sevikkk/valurap/zcad/examples/vitamins.png

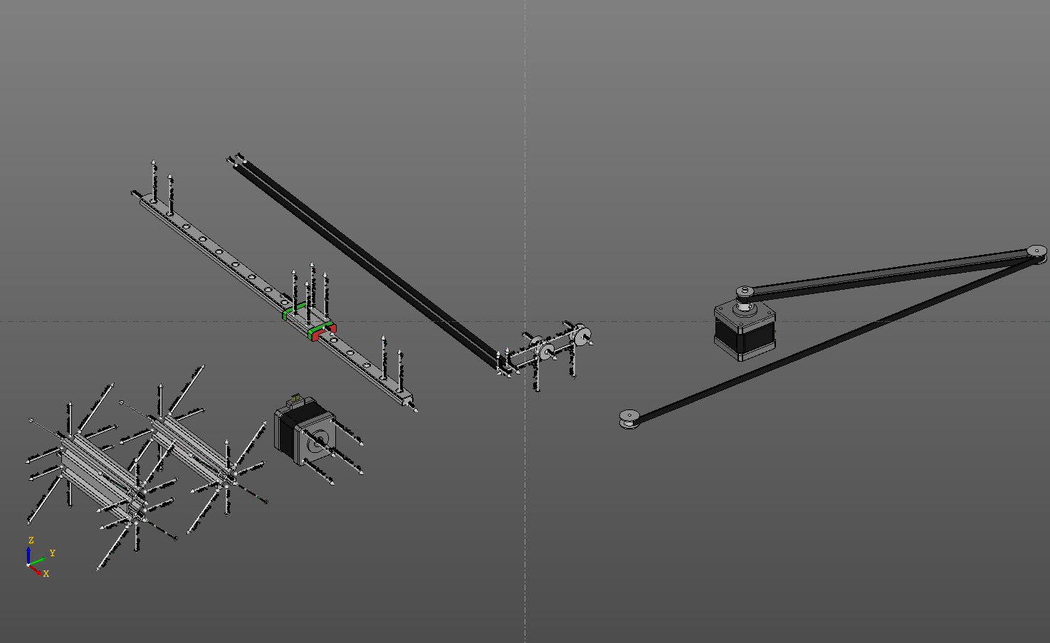
zcad/examples/vitamins.png
