sevikkk/valurap/freecad/vitamins/tcst2103.FCStd

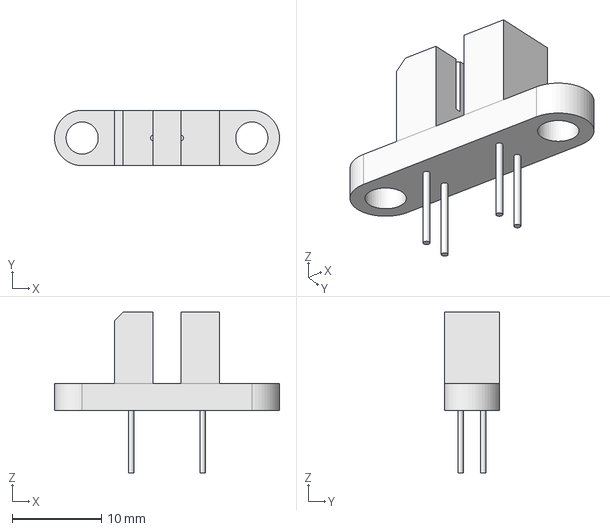
[picture p22: CAD file, 2019-09-13]
freecad/vitamins/tcst2103.FCStd
25.2 x 6.20 x 18.0 mm
