sevikkk/valurap/freecad/steppers_board_mount.FCStd

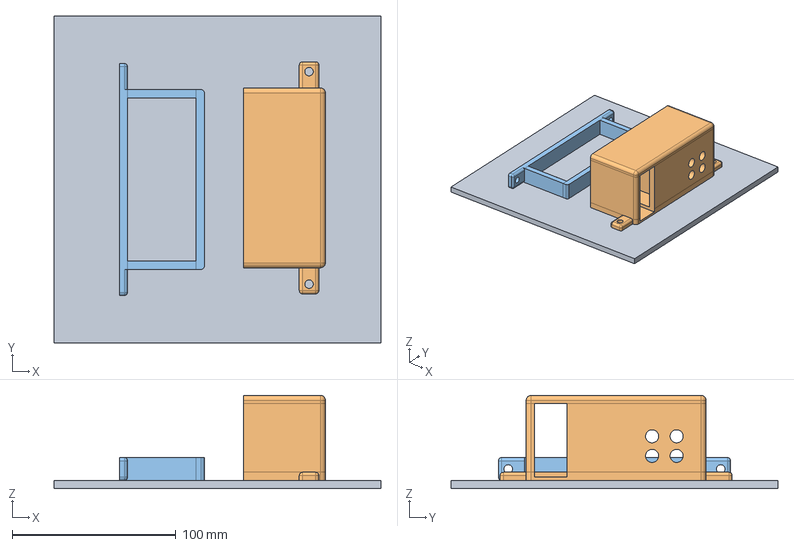
[picture p23: CAD file, 2019-10-19]
freecad/steppers_board_mount.FCStd
200.0 x 200.0 x 57.0 mm
print_plate
psu_front_mount_print
psu_back_mount_print
