sevikkk/valurap/freecad/vitamins/gp1s51.FCStd

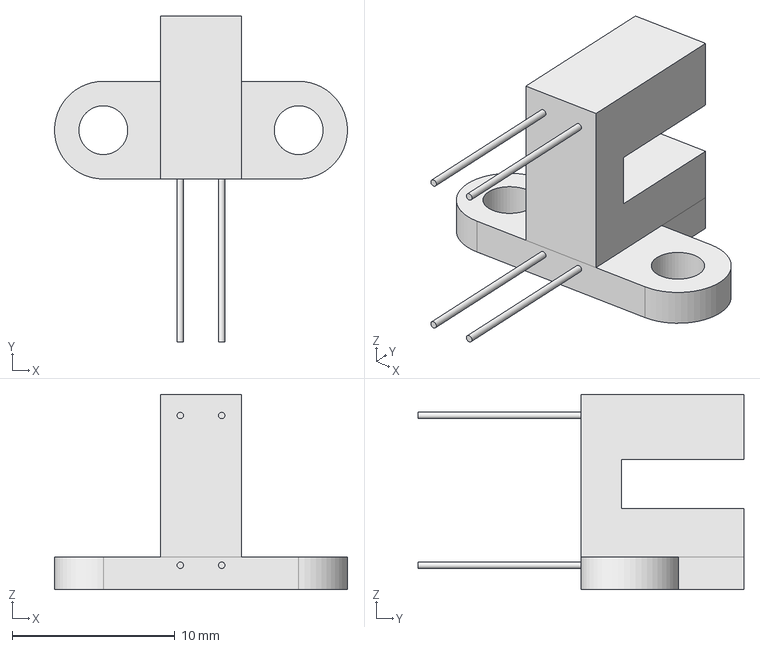
[picture p24: CAD file, 2019-09-01]
freecad/vitamins/gp1s51.FCStd
18.0 x 20.0 x 12.0 mm
