sevikkk/valurap/freecad/titan_mount_plate.FCStd

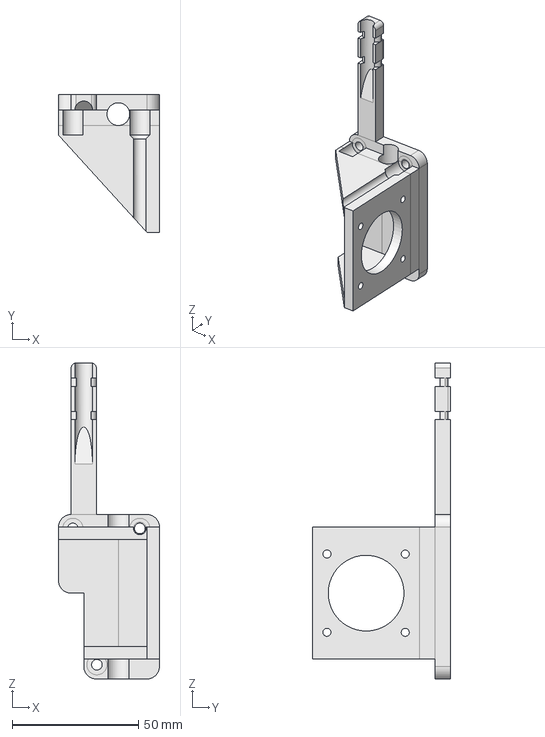
[picture p25: CAD file, 2019-10-13]
freecad/titan_mount_plate.FCStd
40.0 x 54.5 x 125.2 mm
