sevikkk/valurap/freecad/vitamins/coupler.FCStd

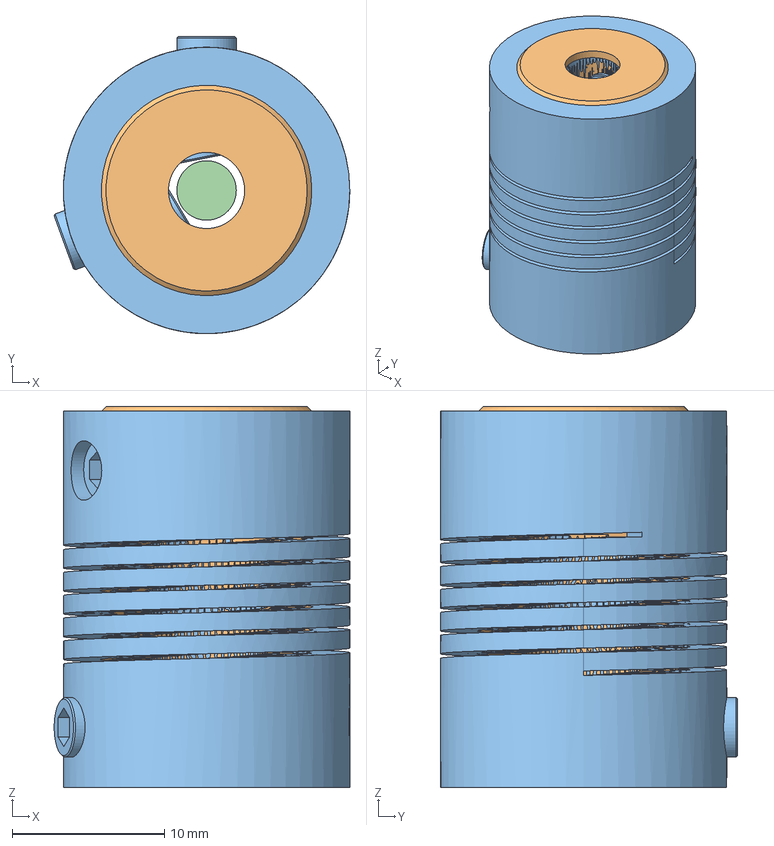
[picture p26: CAD file, 2019-09-01]
freecad/vitamins/coupler.FCStd
19.4 x 19.5 x 25.0 mm
coupling-compound
setscrew-body
