sevikkk/valurap/freecad/left_y_idler_plate.FCStd

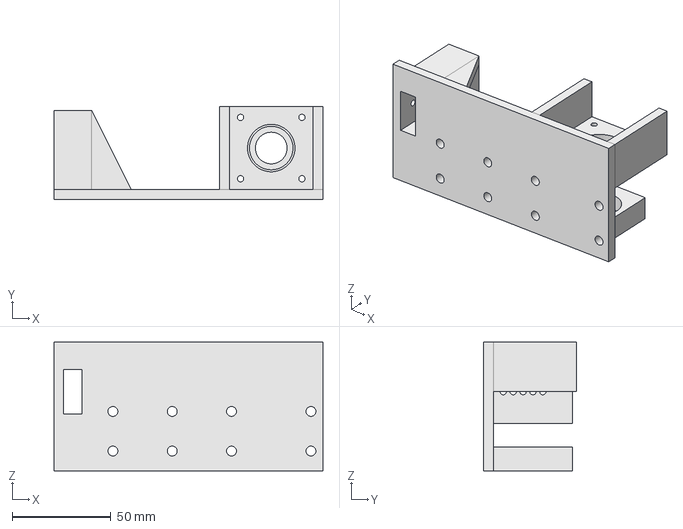
[picture p27: CAD file, 2019-10-13]
freecad/left_y_idler_plate.FCStd
135.9 x 47.0 x 65.0 mm
