sevikkk/valurap/freecad/x_carriage_plate.FCStd

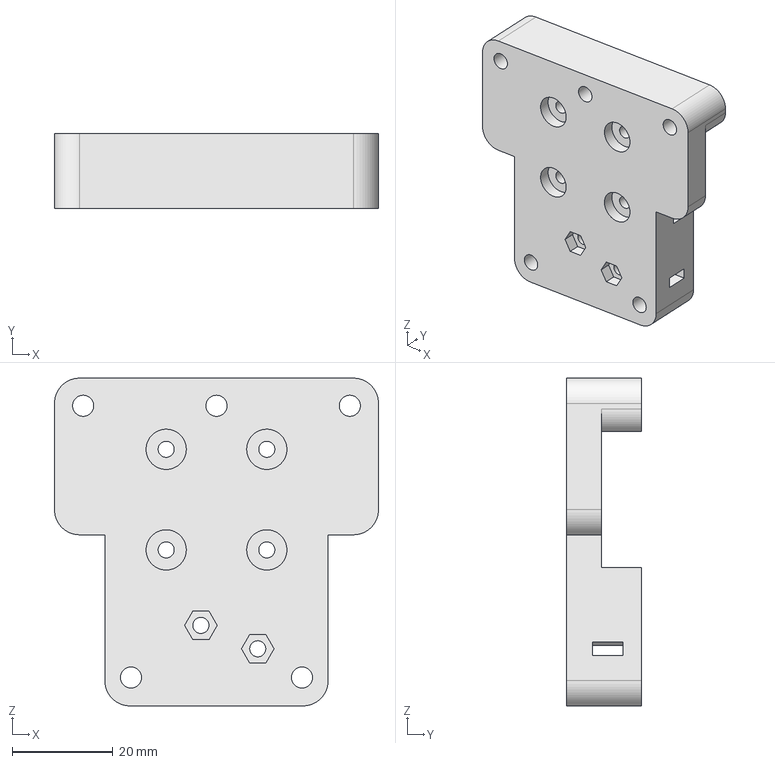
[picture p28: CAD file, 2019-10-13]
freecad/x_carriage_plate.FCStd
64.4 x 15.0 x 65.2 mm
