sevikkk/valurap/scad/prints-x-end.scad

include <x-end-plate.scad>

translate([0,0,-12.5]) rotate([0,0,0]) x_end_plate(25, 14, 25, 3);
translate([90,0,-35]) rotate([0,0,0]) x_end_top(25, 14, 25, 3);
