sevikkk/valurap/stm_soft/stm_thermo/code/task_thermo.c

//
// Created by Vsevolod Lobko on 02.11.2019.
//

#include <stdio.h>
#include <math.h>

int __errno;

#include "main.h"
#include "cmsis_os.h"
#include "cmdline.h"
#include "hardware.h"

volatile int32_t pid_targets[3] = {0, 0, 0};
volatile double pid_integrals[3];
volatile int32_t pid_k_i[3] = {400, 400, 400};
volatile int32_t pid_k_p[3] = {20000, 20000, 20000};

volatile int32_t k_type_temp = 0;
volatile int32_t adc_reads[5];
volatile int32_t ext_values[3];
volatile int32_t fan_values[3];
volatile int32_t adc_temps[3];
volatile int32_t heatbed_value = 0;

int32_t ech_ids[3] = {
    TIM_CHANNEL_1,
    TIM_CHANNEL_2,
    TIM_CHANNEL_3,
};

int32_t fch_ids[3] = {
    TIM_CHANNEL_3,
    TIM_CHANNEL_2,
    TIM_CHANNEL_1,
};

void set_fan_value(int32_t ch, int32_t val);

void StartThermoRead(void const* argument) {
    uint8_t in_buffer[2];
    uint8_t out_buffer[2];
    uint32_t adc_vals[5];
    uint32_t channels[5] = {ADC_CHANNEL_0, ADC_CHANNEL_4, ADC_CHANNEL_5,
                            ADC_CHANNEL_TEMPSENSOR, ADC_CHANNEL_VREFINT};
    ADC_ChannelConfTypeDef sConfig = {0};
    int i, j;

    TickType_t last_wake;

#define PID_CYCLE 400
#define PID_ADC_SUPERSAMPLE 250

    last_wake = xTaskGetTickCount() + 33;

    for (;;) {
        HAL_GPIO_WritePin(SPI1_NSS_GPIO_Port, SPI1_NSS_Pin, GPIO_PIN_RESET);
        HAL_SPI_TransmitReceive(&hspi1, out_buffer, in_buffer, 2, 1000);
        HAL_GPIO_WritePin(SPI1_NSS_GPIO_Port, SPI1_NSS_Pin, GPIO_PIN_SET);
        k_type_temp = (((uint32_t)in_buffer[0] << 8u) | (uint32_t)in_buffer[1]);

        for (i = 0; i < 5; i++) adc_vals[i] = 0;

        for (j = 0; j < PID_ADC_SUPERSAMPLE; j++)
            for (i = 0; i < 5; i++) {
                sConfig.Channel = channels[i];
                sConfig.Rank = ADC_REGULAR_RANK_1;
                sConfig.SamplingTime = ADC_SAMPLETIME_41CYCLES_5;
                HAL_ADC_ConfigChannel(&hadc1, &sConfig);
                HAL_ADC_Start(&hadc1);
                if (HAL_ADC_PollForConversion(&hadc1, 1000000) == HAL_OK) {
                    adc_vals[i] += HAL_ADC_GetValue(&hadc1);
                } else {
                    adc_vals[i] += 9999;
                }
                HAL_ADC_Stop(&hadc1);
            }

        for (i = 0; i < 5; i++) {
            adc_reads[i] = adc_vals[i] / PID_ADC_SUPERSAMPLE;
        }

        for (i = 0; i < 3; i++) {
            double adc = (double) adc_vals[i] / (double)PID_ADC_SUPERSAMPLE;
            // ext1: 10211.569233868902 4.081041224040854 -292.90712330869326 -2194.2350864642244

            double temp = (10157.98 + 4.051241 * adc - 290.5820 * sqrt(adc) - adc * adc/2209.283)/32.0;
            adc_temps[i] = (long)temp;

            double pid_error = (double)pid_targets[i] - temp;
            int control_value = 0;

            if (pid_error > 20) {
                control_value = 1000;
                pid_integrals[i] = 2500;
            } else if (pid_error < -20) {
                control_value = 0;
                pid_integrals[i] = 0;
            } else {
                double new_pid_integral = pid_integrals[i];

                new_pid_integral += pid_error;

                if (new_pid_integral > 5000.0) new_pid_integral = 5000.0;
                if (new_pid_integral < -5000.0) new_pid_integral = -5000.0;

                pid_integrals[i] = new_pid_integral;
                control_value = (long)(new_pid_integral * pid_k_i[i] + pid_error * pid_k_p[i]) / 1000;
            }
            if (control_value > 970) control_value = 1000;
            if (control_value < 10) control_value = 0;

            if (i < 2)
                __HAL_TIM_SET_COMPARE(&htim3, ech_ids[i], control_value);
            else
                heatbed_value = control_value;
        }

        for (i = 0; i < 3; i++) {
            ext_values[i] = __HAL_TIM_GET_COMPARE(&htim3, ech_ids[i]);
            fan_values[i] = __HAL_TIM_GET_COMPARE(&htim1, fch_ids[i]);
        }
        vTaskDelayUntil(&last_wake, PID_CYCLE);
    }
}

void StartHeatBedPWM(void const* argument) {
    TickType_t last_wake;
    int32_t current_cycle = 0;
#define HEATBED_CYCLE 5000

    last_wake = xTaskGetTickCount() + 33;

    for (;;) {
        current_cycle = heatbed_value * HEATBED_CYCLE / 1000;
        if (current_cycle >= HEATBED_CYCLE - 10) {
            HAL_GPIO_WritePin(GPIOC, GPIO_PIN_14, GPIO_PIN_SET);
            vTaskDelayUntil(&last_wake, HEATBED_CYCLE);
        } else if (current_cycle > 10) {
            HAL_GPIO_WritePin(GPIOC, GPIO_PIN_14, GPIO_PIN_SET);
            vTaskDelayUntil(&last_wake, current_cycle);
            HAL_GPIO_WritePin(GPIOC, GPIO_PIN_14, GPIO_PIN_RESET);
            vTaskDelayUntil(&last_wake, HEATBED_CYCLE - current_cycle);
        } else {
            HAL_GPIO_WritePin(GPIOC, GPIO_PIN_14, GPIO_PIN_RESET);
            vTaskDelayUntil(&last_wake, HEATBED_CYCLE);
        };
    }
}

void sepFunction(void) {
    int32_t psc;
    psc = cmdlineGetArgInt(1);
    __HAL_TIM_SET_PRESCALER(&htim3, psc);
}

void sfpFunction(void) {
    int32_t psc;
    psc = cmdlineGetArgInt(1);
    __HAL_TIM_SET_PRESCALER(&htim1, psc);
}

void sevFunction(void) {
    int32_t ch;
    int32_t val;

    ch = cmdlineGetArgInt(1);
    val = cmdlineGetArgInt(2);
    if (ch > 0 && ch <= 3) __HAL_TIM_SET_COMPARE(&htim3, ech_ids[ch - 1], val);
}

void sfvFunction(void) {
    int32_t ch;
    int32_t val;

    ch = cmdlineGetArgInt(1);
    val = cmdlineGetArgInt(2);
    if (ch > 0 && ch <= 3) set_fan_value(ch, val);
}

void set_fan_value(int32_t ch, int32_t val) { __HAL_TIM_SET_COMPARE(&htim1, fch_ids[ch - 1], val); }

void sptFunction(void) {
    int32_t ch;
    int32_t val;

    ch = cmdlineGetArgInt(1);
    val = cmdlineGetArgInt(2);
    if (ch > 0 && ch <= 3) {
        pid_targets[ch - 1] = val;
        pid_integrals[ch - 1] = 0;
    }
}

void sppFunction(void) {
    int32_t ch;
    int32_t val_p;
    int32_t val_i;

    ch = cmdlineGetArgInt(1);
    val_p = cmdlineGetArgInt(2);
    val_i = cmdlineGetArgInt(3);
    if (ch > 0 && ch <= 3) {
        pid_k_p[ch - 1] = val_p;
        pid_k_i[ch - 1] = val_i;
        pid_integrals[ch - 1] = 0;
    }
}

void shpidFunction(void) {
    int32_t ch;

    ch = cmdlineGetArgInt(1);
    if (ch <= 0 || ch > 3) return;

    printf("pid_k_p: %ld\n", pid_k_p[ch - 1]);
    printf("pid_k_i: %ld\n", pid_k_i[ch - 1]);
    printf("integral: %ld\n", (long)pid_integrals[ch - 1]);
    fflush(0);
}
