sevikkk/valurap/fpga/src/s3g_executor.v

module s3g_executor(
    input clk,
    input rst,

    // s3g_rx interface
    input rx_packet_done,
    input rx_packet_error,
    input rx_buffer_valid,

    input [7:0] rx_payload_len,
    input [7:0] rx_buf0,
    input [7:0] rx_buf1,
    input [7:0] rx_buf2,
    input [7:0] rx_buf3,
    input [7:0] rx_buf4,
    input [7:0] rx_buf5,
    input [7:0] rx_buf6,
    input [7:0] rx_buf7,
    input [7:0] rx_buf8,
    input [7:0] rx_buf9,
    input [7:0] rx_buf10,
    input [7:0] rx_buf11,
    input [7:0] rx_buf12,
    input [7:0] rx_buf13,
    input [7:0] rx_buf14,
    input [7:0] rx_buf15,

    output reg [7:0] next_rx_buffer_addr,
    input [7:0] rx_buffer_data,

    // s3g_tx interface
    input tx_busy,
    output reg tx_packet_wr,

    output reg [7:0] tx_payload_len,
    output reg [7:0] tx_buf0,
    output reg [7:0] tx_buf1,
    output reg [7:0] tx_buf2,
    output reg [7:0] tx_buf3,
    output reg [7:0] tx_buf4,
    output reg [7:0] tx_buf5,
    output reg [7:0] tx_buf6,
    output reg [7:0] tx_buf7,
    output reg [7:0] tx_buf8,
    output reg [7:0] tx_buf9,
    output reg [7:0] tx_buf10,
    output reg [7:0] tx_buf11,
    output reg [7:0] tx_buf12,
    output reg [7:0] tx_buf13,
    output reg [7:0] tx_buf14,
    output reg [7:0] tx_buf15,

    // output_registers
    output reg [31:0] out_reg0,
    output reg [31:0] out_reg1,
    output reg [31:0] out_reg2,
    output reg [31:0] out_reg3,
    output reg [31:0] out_reg4,
    output reg [31:0] out_reg5,
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
    input int21,
    input int22,
    input int23,
    input int24,
    input int25,
    input int26,
    input int27,
    input int28,
    input int29,
    input int30,
    input int31,

    output reg [39:0] ext_fifo_data,
    output reg ext_fifo_wr,
    input [31:0] ext_fifo_free_space,

    input [5:0] ext_out_reg_addr,
    input [31:0] ext_out_reg_data,
    input ext_out_reg_stb,
    output ext_out_reg_busy,
    input [31:0] ext_out_stbs,
    input [31:0] ext_clear_ints,
    output [31:0] ext_pending_ints
);

    parameter EXT_VER_1=8'h02;
    parameter EXT_VER_2=8'h00;
    parameter EXT_VER_3=8'h02;
    parameter EXT_VER_4=8'h00;
    parameter EXT_VER_5=8'hCE;
    parameter EXT_VER_6=8'h00;
    parameter EXT_VER_7=8'h00;
    parameter EXT_VER_8=8'h00;

    localparam
        CMD_NONE=0, CMD_OK=1, CMD_ERROR=2, CMD_UNKNOWN=3, CMD_READ_REG=4,
        CMD_VERSION=5, CMD_EXT_VERSION=6, CMD_WR_BUF_OK=8, CMD_WR_BUF_ERR=9;

    localparam
        S_INIT=0, S_DELAY=1, S_BUSY=2, S_READ=3, S_READ1=4,
        S_BUFFER0=5, S_BUFFER1=6, S_BUFFER2=7, S_BUFFER3=8,
        S_BUFFER4=9, S_BUFFER5=10, S_BUFFER6=11, S_BUFFER_WAIT=12;

    reg [3:0] state = S_INIT;
    reg [3:0] next_state;

    reg [3:0] tx_cmd;
    reg [3:0] next_tx_cmd;

    reg [5:0] int_out_reg_addr;
    reg [31:0] int_out_reg_data;
    reg int_out_reg_stb;

    wire [5:0] out_reg_addr;
    wire [31:0] out_reg_data;
    wire out_reg_stb;

    reg [31:0] next_out_stbs;

    reg [5:0] next_in_mux;
    reg [5:0] in_mux;
    reg [31:0] in_data;

    wire [31:0] ints_vector;
    reg [31:0] ints_pending;
    reg [31:0] ints_mask;
    reg [31:0] next_ints_mask;
    reg [31:0] ints_to_clear;

    reg [7:0] rx_buffer_addr;
    reg [39:0] next_ext_fifo_data;
    reg next_ext_fifo_wr;

    reg [7:0] word_cnt;
    reg [7:0] next_word_cnt;

    reg [15:0] saved_cmd_id;
    reg [15:0] next_saved_cmd_id;

    assign ints_vector = {
        int31, int30, int29, int28, int27, int26, int25, int24,
        int23, int22, int21, int20, int19, int18, int17, int16,
        int15, int14, int13, int12, int11, int10, int9, int8,
        int7, int6, int5, int4, int3, int2, int1, int0};

    always @(posedge clk)
        begin
            if (rst)
                ints_pending <= 0;
            else
                ints_pending <= (ints_pending & ~(ints_to_clear | ext_clear_ints)) | ints_vector;
        end

    assign ext_pending_ints = ints_pending;

    always @(posedge clk)
        begin
            if (rst)
                begin
                    out_stbs <= 0;
                    ints_mask <= 32'hFFFFFFFF;
                    in_mux <= 0;
                    rx_buffer_addr <= 0;
                    word_cnt <= 0;
                    ext_fifo_data <= 0;
                    ext_fifo_wr <= 0;
                    saved_cmd_id <= 16'hFFFF;
                    tx_cmd <= CMD_NONE;
                end
            else
                begin
                    out_stbs <= next_out_stbs | ext_out_stbs;
                    ints_mask <= next_ints_mask;
                    in_mux <= next_in_mux;
                    rx_buffer_addr <= next_rx_buffer_addr;
                    word_cnt <= next_word_cnt;
                    ext_fifo_data <= next_ext_fifo_data;
                    ext_fifo_wr <= next_ext_fifo_wr;
                    saved_cmd_id <= next_saved_cmd_id;
                    tx_cmd <= next_tx_cmd;
                end

            in_data <= 0;
            case (in_mux)
                0: in_data <= in_reg0;
                1: in_data <= in_reg1;
                2: in_data <= in_reg2;
                3: in_data <= in_reg3;
                4: in_data <= in_reg4;
                5: in_data <= in_reg5;
                6: in_data <= in_reg6;
                7: in_data <= in_reg7;
                8: in_data <= in_reg8;
                9: in_data <= in_reg9;
                10: in_data <= in_reg10;
                11: in_data <= in_reg11;
                12: in_data <= in_reg12;
                13: in_data <= in_reg13;
                14: in_data <= in_reg14;
                15: in_data <= in_reg15;
                16: in_data <= in_reg16;
                17: in_data <= in_reg17;
                18: in_data <= in_reg18;
                19: in_data <= in_reg19;
                20: in_data <= in_reg20;
                21: in_data <= in_reg21;
                22: in_data <= in_reg22;
                23: in_data <= in_reg23;
                24: in_data <= in_reg24;
                25: in_data <= in_reg25;
                26: in_data <= in_reg26;
                27: in_data <= in_reg27;
                28: in_data <= in_reg28;
                29: in_data <= in_reg29;
                30: in_data <= in_reg30;
                31: in_data <= in_reg31;
                32: in_data <= in_reg32;
                33: in_data <= in_reg33;
                34: in_data <= in_reg34;
                35: in_data <= in_reg35;
                36: in_data <= in_reg36;
                37: in_data <= in_reg37;
                38: in_data <= in_reg38;
                39: in_data <= in_reg39;
                40: in_data <= in_reg40;
                41: in_data <= in_reg41;
                42: in_data <= in_reg42;
                43: in_data <= in_reg43;
                44: in_data <= in_reg44;
                45: in_data <= in_reg45;
                46: in_data <= in_reg46;
                47: in_data <= in_reg47;
                48: in_data <= in_reg48;
                49: in_data <= in_reg49;
                50: in_data <= in_reg50;
                51: in_data <= in_reg51;
                52: in_data <= in_reg52;
                53: in_data <= in_reg53;
                54: in_data <= in_reg54;
                55: in_data <= in_reg55;
                56: in_data <= in_reg56;
                57: in_data <= in_reg57;
                58: in_data <= in_reg58;
                59: in_data <= in_reg59;
                60: in_data <= in_reg60;
                61: in_data <= in_reg61;
                62: in_data <= in_reg62;
                63: in_data <= in_reg63;
            endcase
        end

    always @(*)
        begin
            next_state <= state;
            next_tx_cmd <= CMD_NONE;
            next_in_mux <= in_mux;
            next_out_stbs <= 0;

            next_ints_mask <= ints_mask;

            int_out_reg_stb <= 0;
            int_out_reg_addr <= 0;
            int_out_reg_data <= 0;

            ints_to_clear <= 0;

            next_rx_buffer_addr <= rx_buffer_addr;
            next_word_cnt <= word_cnt;
            next_ext_fifo_data <= ext_fifo_data;
            next_ext_fifo_wr <= 0;

            next_saved_cmd_id <= saved_cmd_id;

            case (state)
                S_INIT:
                    begin
                        if (rx_packet_done)
                            begin
                                next_tx_cmd <= CMD_UNKNOWN;
                                next_state <= S_DELAY;
                                next_saved_cmd_id <= {rx_buf1, rx_buf0};
                                if (rx_payload_len == 0)
                                    begin
                                        next_tx_cmd <= CMD_OK;
                                    end
                                else
                                    case (rx_buf2)
                                        0:
                                            next_tx_cmd <= CMD_VERSION;
                                        27:
                                            next_tx_cmd <= CMD_EXT_VERSION;
                                        60: // WRITE_OUT_REG
                                            begin
                                                int_out_reg_stb <= 1;
                                                int_out_reg_addr <= rx_buf3;
                                                int_out_reg_data <= {rx_buf7, rx_buf6, rx_buf5, rx_buf4};
                                                next_tx_cmd <= CMD_OK;
                                            end
                                        61: // READ_IN_REG
                                            begin
                                                next_in_mux <= rx_buf3;
                                                next_state <= S_READ;
                                                next_tx_cmd <= CMD_NONE;
                                            end
                                        62: // OUT_STBS
                                            begin
                                                next_out_stbs <= {rx_buf6, rx_buf5, rx_buf4, rx_buf3};
                                                next_tx_cmd <= CMD_OK;
                                            end
                                        63: // CLEAR_INTS
                                            begin
                                                ints_to_clear <= {rx_buf6, rx_buf5, rx_buf4, rx_buf3};
                                                next_tx_cmd <= CMD_OK;
                                            end
                                        64: // MASK_INTS
                                            begin
                                                next_ints_mask <= {rx_buf6, rx_buf5, rx_buf4, rx_buf3};
                                                next_tx_cmd <= CMD_OK;
                                            end
                                        // 65: Not implemented
                                        66: // WRITE_FIFO
                                            begin
                                                next_rx_buffer_addr <= 4;
                                                next_word_cnt <= rx_buf3;
                                                if (rx_buf3 == 0)
                                                    begin
                                                        next_state <= S_DELAY;
                                                        next_tx_cmd <= CMD_WR_BUF_OK;
                                                    end
                                                else
                                                    begin
                                                        next_tx_cmd <= CMD_NONE;
                                                        if (ext_fifo_free_space >= {{24{1'b0}}, rx_buf3})
                                                            begin
                                                                next_state <= S_BUFFER0;
                                                            end
                                                        else begin
                                                            next_state <= S_BUFFER_WAIT;
                                                        end
                                                    end
                                            end
                                    endcase
                            end
                        else if (rx_packet_error)
                            begin
                                next_tx_cmd <= CMD_ERROR;
                                next_state <= S_DELAY;
                            end
                    end
                S_DELAY:
                    begin
                        next_state <= S_BUSY;
                    end
                S_BUSY:
                    begin
                        if (!tx_busy)
                            next_state <= S_INIT;
                    end
                S_READ:
                    begin
                        next_state <= S_READ1;
                    end
                S_READ1:
                    begin
                        next_state <= S_DELAY;
                        next_tx_cmd <= CMD_READ_REG;
                    end
                S_BUFFER_WAIT:
                    begin
                        if (!rx_buffer_valid)
                            begin
                                next_state <= S_DELAY;
                                next_tx_cmd <= CMD_WR_BUF_ERR;
                            end
                        else if (ext_fifo_free_space >= {{24{1'b0}}, word_cnt})
                            begin
                                next_state <= S_BUFFER0;
                            end
                    end
                S_BUFFER0:
                    begin
                        next_state <= S_BUFFER1;
                        next_rx_buffer_addr <= rx_buffer_addr+1;
                        next_ext_fifo_data[7:0] <= rx_buffer_data;
                    end
                S_BUFFER1:
                    begin
                        next_state <= S_BUFFER2;
                        next_rx_buffer_addr <= rx_buffer_addr+1;
                        next_ext_fifo_data[15:8] <= rx_buffer_data;
                    end
                S_BUFFER2:
                    begin
                        next_state <= S_BUFFER3;
                        next_rx_buffer_addr <= rx_buffer_addr+1;
                        next_ext_fifo_data[23:16] <= rx_buffer_data;
                    end
                S_BUFFER3:
                    begin
                        next_state <= S_BUFFER4;
                        next_rx_buffer_addr <= rx_buffer_addr+1;
                        next_ext_fifo_data[31:24] <= rx_buffer_data;
                    end
                S_BUFFER4:
                    begin
                        next_ext_fifo_data[39:32] <= rx_buffer_data;
                        next_word_cnt <= word_cnt-1;
                        if (rx_buffer_valid)
                            begin
                                next_ext_fifo_wr <= 1;
                                next_state <= S_BUFFER5;
                            end
                        else
                            begin
                                next_state <= S_DELAY;
                                next_tx_cmd <= CMD_WR_BUF_ERR;
                            end

                    end
                S_BUFFER5:
                    begin
                        if (word_cnt == 0)
                            begin
                                next_state <= S_BUFFER6;
                            end
                        else
                            begin
                                next_rx_buffer_addr <= rx_buffer_addr+1;
                                next_state <= S_BUFFER0;
                                next_ext_fifo_data <= 0;
                            end
                    end
                S_BUFFER6:
                    begin
                        next_state <= S_DELAY;
                        next_tx_cmd <= CMD_WR_BUF_OK;
                    end
                default:
                    next_state <= S_INIT;
            endcase
        end


    always @(posedge clk)
        begin
            if (rst)
                state <= S_INIT;
            else
                state <= next_state;
        end

    always @(posedge clk)
        begin

            tx_packet_wr <= 0;

            tx_payload_len <= 0;
            tx_buf0 <= saved_cmd_id[7:0];
            tx_buf1 <= saved_cmd_id[15:8];
            tx_buf2 <= 0;
            tx_buf3 <= 0;
            tx_buf4 <= 0;
            tx_buf5 <= 0;
            tx_buf6 <= 0;
            tx_buf7 <= 0;
            tx_buf8 <= 0;
            tx_buf9 <= 0;
            tx_buf10 <= 0;
            tx_buf11 <= 0;
            tx_buf12 <= 0;
            tx_buf13 <= 0;
            tx_buf14 <= 0;
            tx_buf15 <= 0;

            case (tx_cmd)
                CMD_OK:
                    begin
                        tx_packet_wr <= 1;
                        tx_payload_len <= 3;
                        tx_buf2 <= 8'h81;
                    end
                CMD_ERROR:
                    begin
                        tx_packet_wr <= 1;
                        tx_payload_len <= 3;
                        tx_buf2 <= 8'h80;
                    end
                CMD_UNKNOWN:
                    begin
                        tx_packet_wr <= 1;
                        tx_payload_len <= 3;
                        tx_buf2 <= 8'h85;
                    end
                CMD_VERSION:
                    begin
                        tx_packet_wr <= 1;
                        tx_payload_len <= 5;
                        tx_buf2 <= 8'h81;
                        tx_buf3 <= 8'hBA;
                        tx_buf4 <= 8'hCE;
                    end
                CMD_EXT_VERSION:
                    begin
                        tx_packet_wr <= 1;
                        tx_payload_len <= 11;
                        tx_buf2 <= 8'h81;
                        tx_buf3 <= EXT_VER_1;
                        tx_buf4 <= EXT_VER_2;
                        tx_buf5 <= EXT_VER_3;
                        tx_buf6 <= EXT_VER_4;
                        tx_buf7 <= EXT_VER_5;
                        tx_buf8 <= EXT_VER_6;
                        tx_buf9 <= EXT_VER_7;
                        tx_buf10 <= EXT_VER_8;
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
                    53: out_reg53 <= out_reg_data;
                    54: out_reg54 <= out_reg_data;
                    55: out_reg55 <= out_reg_data;
                    56: out_reg56 <= out_reg_data;
                    57: out_reg57 <= out_reg_data;
                    58: out_reg58 <= out_reg_data;
                    59: out_reg59 <= out_reg_data;
                    60: out_reg60 <= out_reg_data;
                    61: out_reg61 <= out_reg_data;
                    62: out_reg62 <= out_reg_data;
                    63: out_reg63 <= out_reg_data;
                endcase
        end

endmodule
