sevikkk/valurap/host_soft/valurap2/valurap2/gcode.py

from collections import namedtuple


do_home = namedtuple("do_home", "cur_pos line_number")
do_extruder = namedtuple("do_extruder", "ext line_number")
do_path = namedtuple("do_path", "mode path")

do_segment = namedtuple("do_segment", "path")
do_move = namedtuple("do_move", "deltas target")
do_ext = namedtuple("do_ext", "deltas")


def reader(fn):
    gc = open(fn)
    while 1:
        line = gc.readline()
        if not line:
            break
        yield line[:-1]


def path_gen(lines):
    relative_extrude_mode = None
    current = {
        "X": 0.0,
        "Y": 0.0,
        "Z": 0.0,
        "E": 0.0
    }
    home_position = {
        "X": 12700.0 / 80,
        "Y": -20000.0 / 80,
        "Z": 20000.0 / 1600,
        "E": 0.0
    }
    current_feed = None

    path = []
    current_mode = None
    line_number = 0
    while 1:
        try:
            line = next(lines)
            line_number += 1
        except StopIteration:
            if path and current_mode:
                yield do_path(current_mode, path)
            break

        if ';' in line:
            line = line.split(';')[0]
        line = line.strip()
        if not line:
            continue

        # print("Line:", l)

        if line[0] == "M":
            parts = line.split()
            code = int(parts[0][1:])
            if code == 82:
                relative_extrude_mode = False
                continue
            elif code == 83:
                relative_extrude_mode = True
                continue
            elif code in (84, 104, 105, 106, 107, 109, 140, 190):
                continue
            else:
                print("{}: Unknown M{} command".format(line_number, code))
                break

        if line[0] == "G":
            parts = line.split()
            code = int(parts[0][1:])
            if code == 28:
                if path and current_mode:
                    yield do_path(current_mode, path)
                current_mode = None
                path = []
                print("Do Home")
                current = home_position.copy()
                yield do_home(current.copy(), line_number)
                continue
            elif code == 92:
                print("Set current", parts[1:])
                abort = False
                for p in parts[1:]:
                    axis = p[0]
                    value = float(p[1:])
                    assert axis == "E"
                    if axis in current:
                        current[axis] = value
                    else:
                        print("{}: Unexpected G92 for {}".format(line_number, p))
                        abort = True
                        break
                if abort:
                    break
                continue
            elif code in (0, 1):
                if path and current_mode != code:
                    yield do_path(current_mode, path)
                    path = []
                current_mode = code
                if not path:
                    path.append(current.copy())
                step = {}
                abort = False
                for p in parts[1:]:
                    axis = p[0]
                    value = float(p[1:])
                    if axis in current:
                        if axis == "E" and relative_extrude_mode:
                            step[axis] = value
                        else:
                            step[axis] = (value - current[axis])
                        current[axis] = value
                    elif axis == "F":
                        current_feed = value
                    else:
                        print("{}: Unexpected G{} for {}".format(line_number, code, p))
                        abort = True
                        break
                if abort:
                    break
                step["F"] = current_feed
                step["line"] = line_number

                path.append(step)
                continue
            else:
                print("{}: Unknown G{} command".format(line_number, code))
                break

        if line[0] == "T":
            parts = line.split()
            code = int(parts[0][1:])
            if code in (0, 1):
                print("Extruder switch to", code)
                if path and current_mode:
                    yield do_path(current_mode, path)
                current_mode = None
                path = []
                yield do_extruder(code, line_number)
                continue

        print("{}: Unknown command: {}".format(line_number, line))
        break


def gen_segments(pg, split_len=None):
    path = [[0, 0, 0, 0]]
    x = 0
    y = 0
    z = 0
    ext = 0
    verify = False

    for gc_path in pg:
        if isinstance(gc_path, do_home):
            if len(path) > 1:
                print("flush current path", len(path))
                path.append([x, y, 0, ext, path[-1][4]])
                yield do_segment(path)
            print("do_home")
            yield do_home(gc_path.cur_pos, gc_path.line_number)
            x = gc_path.cur_pos["X"]
            y = gc_path.cur_pos["Y"]
            z = gc_path.cur_pos["Z"]
            path = [[x, y, 0, ext, gc_path.line_number]]
        elif isinstance(gc_path, do_path):
            if verify:
                print("do_path", gc_path.mode, len(gc_path.path))

                print("   x:", x, gc_path.path[0]["X"])
                print("   y:", y, gc_path.path[0]["Y"])
                print("   z:", z, gc_path.path[0]["Z"])
            assert (abs(x - gc_path.path[0]["X"]) < 0.1)
            assert (abs(y - gc_path.path[0]["Y"]) < 0.1)
            assert (abs(z - gc_path.path[0]["Z"]) < 0.1)

            gc_segment = gc_path.path[1:]
            for i, p in enumerate(gc_segment):
                if ("Z" in p) or (("X" not in p) and ("Y" not in p)):
                    if len(path) > 1:
                        path.append([x, y, 0, ext, path[-1][4]])
                        yield do_segment(path)

                    deltas = {}
                    deltas_ext = {}
                    if "X" in p:
                        dx = p["X"]
                        x += dx
                        deltas["X"] = dx
                    if "Y" in p:
                        dy = p["Y"]
                        y += dy
                        deltas["Y"] = dy
                    if "Z" in p:
                        dz = p["Z"]
                        z += dz
                        deltas["Z"] = dz
                    if "E" in p:
                        de = -p.get("E", 0)
                        ext += de
                        deltas_ext["E"] = de

                    if deltas:
                        assert not deltas_ext
                        if "F" in p:
                            deltas["F"] = p["F"]
                        if "line" in p:
                            deltas["line"] = p["line"]
                        yield do_move(deltas, {"X": x, "Y": y, "Z": z})

                    if deltas_ext:
                        if "F" in p:
                            deltas_ext["F"] = p["F"]
                        if "line" in p:
                            deltas_ext["line"] = p["line"]

                        yield do_ext(deltas_ext)

                    path = [[x, y, 0, ext, p["line"]]]
                else:
                    dx = p["X"]
                    dy = p["Y"]
                    de = -p.get("E", 0)
                    speed = p["F"] / 60.0
                    line = p["line"]

                    x += dx
                    y += dy
                    ext += de
                    path.append([x, y, speed, ext, line])

                    if split_len and len(path) > split_len:
                        path.append([x, y, 0, ext, path[-1][4]])

                        yield do_segment(path)

                        path = [[x, y, 0, ext, path[-1][4]]]
        elif isinstance(gc_path, do_extruder):
            if len(path) > 1:
                print("flush current path", len(path))
                path.append([x, y, 0, ext, path[-1][4]])
                yield do_segment(path)
            path = [[x, y, 0, ext, gc_path.line_number]]
            print("do_extruder")
            yield do_extruder(gc_path.ext, gc_path.line_number)
        else:
            print("unexpected event", gc_path)
            raise RuntimeError

    if len(path) > 1:
        print("flush remaining path", len(path))
        path.append([x, y, 0, ext, path[-1][4]])

        yield do_segment(path)


def file_reader(fn):
    lines = reader(fn)
    pg = path_gen(lines)
    return gen_segments(pg)
