sevikkk/valurap/host_soft/valurap/valurap/scripts/export_cura_settings.py

import configparser
import os
import os.path
import urllib.parse

CURA_CFGS = '~/Library/Application Support/cura/4.5'


def main():
    cfgs = []
    cura_folder = os.path.expanduser(CURA_CFGS)
    for fn, dirs, files in os.walk(cura_folder):
        short_fn = fn[len(cura_folder)+1:]
        if fn == cura_folder:
            if '.git' in dirs:
                dirs.remove('.git')
            if 'cache' in dirs:
                dirs.remove('cache')
        for f in files:
            if f.endswith('.cfg'):
                cfgs.append(os.path.join(short_fn, f))

    data = {}
    used = {}
    machines = {}
    extruders = {}
    settings = {}

    for fn in sorted(cfgs):
        plain_fn = tuple(urllib.parse.unquote(fn).replace('+', " ").split('/'))
        if plain_fn == ("cura.cfg",):
            continue

        cf = configparser.ConfigParser()
        cf.read(os.path.join(cura_folder, fn))
        ok = 1
        if "containers" in cf:
            ok = 1
        if "values" in cf and cf["values"]:
            ok = 1

        if ok:
            if 1:
                print(plain_fn)
                for s in sorted(cf.sections()):
                    print("  ", s)
                    for k in sorted(cf[s].keys()):
                        v = cf[s][k]
                        print("    ", k, v)
            data[plain_fn] = cf
            used[plain_fn] = 0

            ft = cf["metadata"]["type"]
            if ft == 'machine':
                machines[cf["general"]["id"]] = plain_fn
            elif ft == 'extruder_train':
                mach = cf["metadata"]["machine"]
                extruders.setdefault(mach, {})[cf["metadata"]["position"]] = plain_fn
            elif ft in ["definition_changes", "user", "quality_changes"]:
                settings[cf["general"]["name"]] = plain_fn
            else:
                raise RuntimeError("Unexpected file type: {}".format(ft))
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
